hipe-0/pre-amplifier/gerber/2024-11-17 Guitar Amp with LM386 IC proto PCB version_etch_silk_bottom.pdf

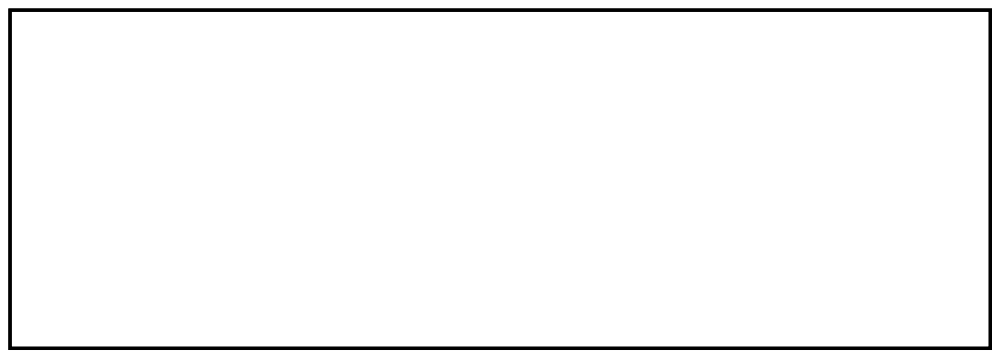
[picture p19: page 1]
