hipe-0/pre-amplifier/gerber/2024-11-17 Guitar Amp with LM386 IC proto PCB version_etch_silk_bottom_mirror.pdf

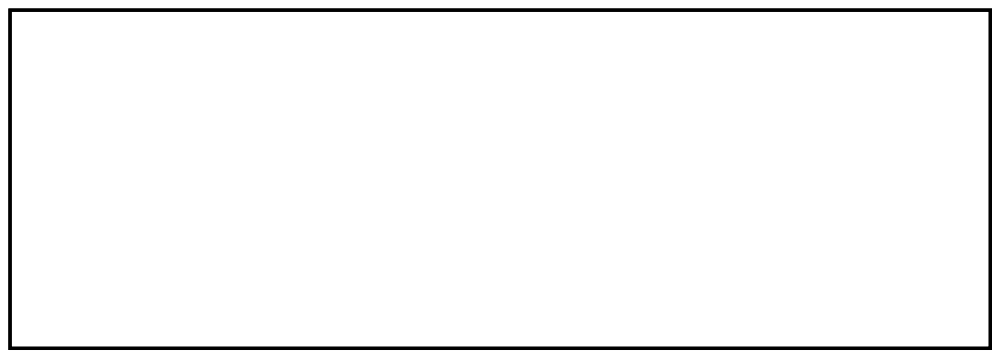
[picture p20: page 1]
