hipe-0/pre-amplifier/gerber/2024-11-17 Guitar Amp with LM386 IC proto PCB version_etch_silk_top_mirror.pdf

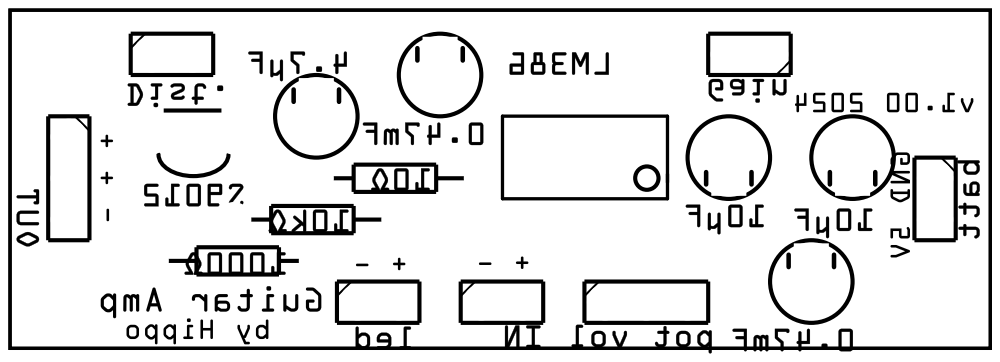
[picture p22: page 1]
