hipe-0/pre-amplifier/media/20241118_213925.jpg

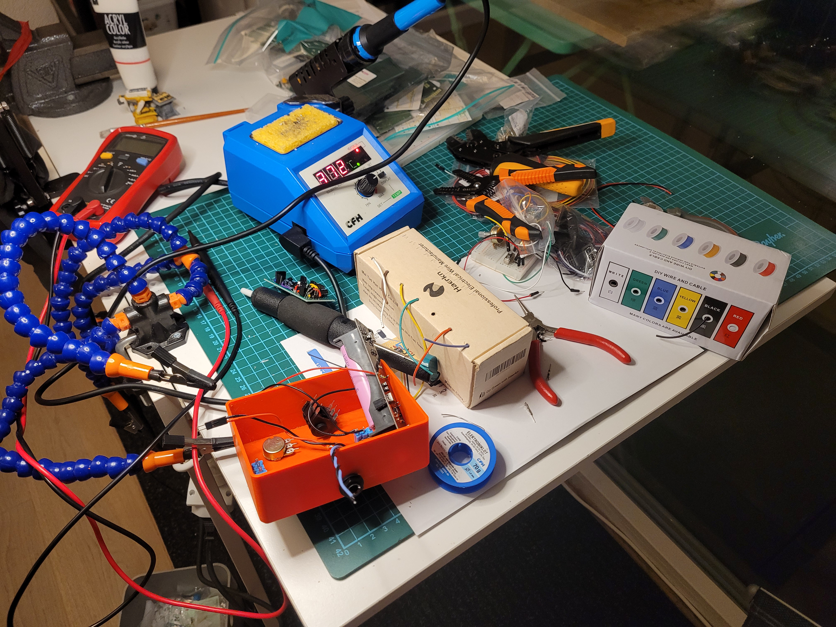
media/20241118_213925.jpg
