hipe-0/pre-amplifier/media/20241119_183656.jpg

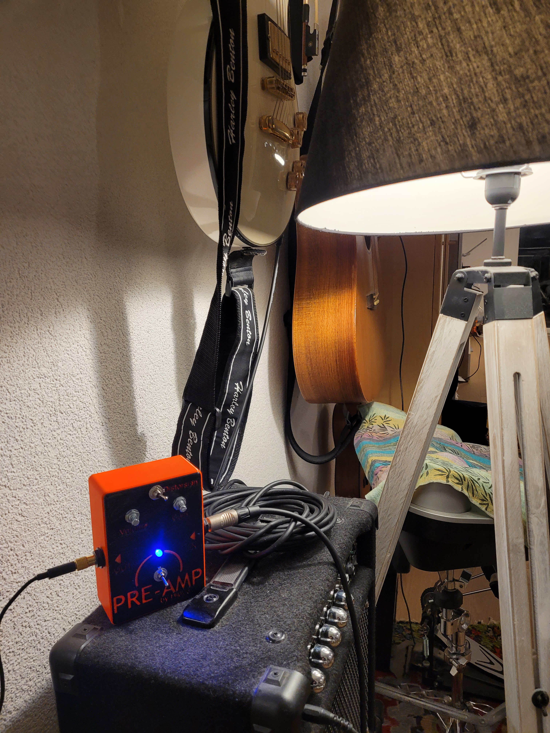
media/20241119_183656.jpg
